Pegoku/buckshot-roulette-irl/images/explosions/Explosion-2.png

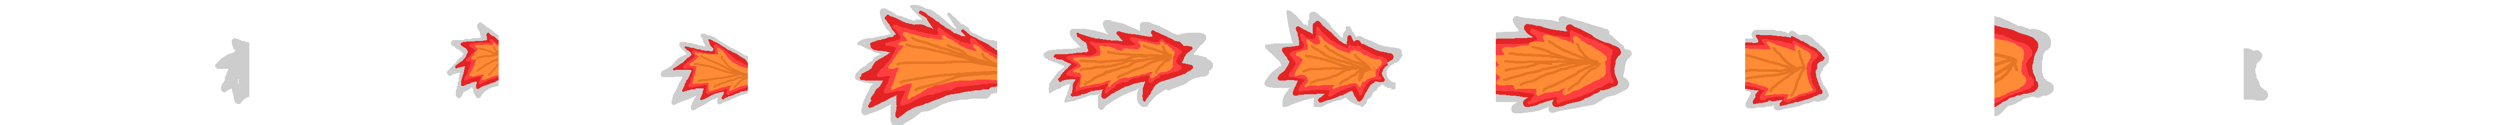
images/explosions/Explosion-2.png
