Pegoku/buckshot-roulette-irl/images/soup's/soup-blue-1.png

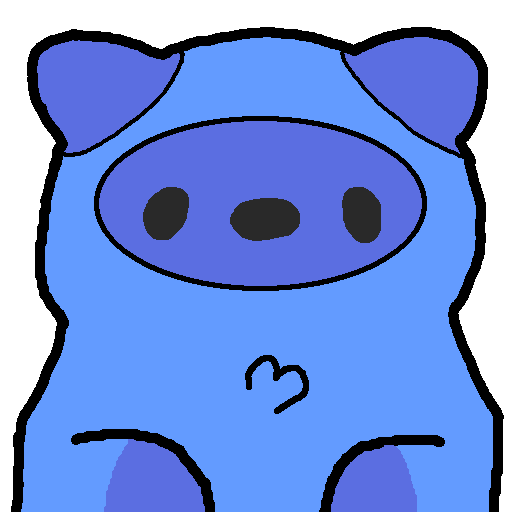
images/soup's/soup-blue-1.png
