Pegoku/buckshot-roulette-irl/images/soup's/soup-blue-2.png

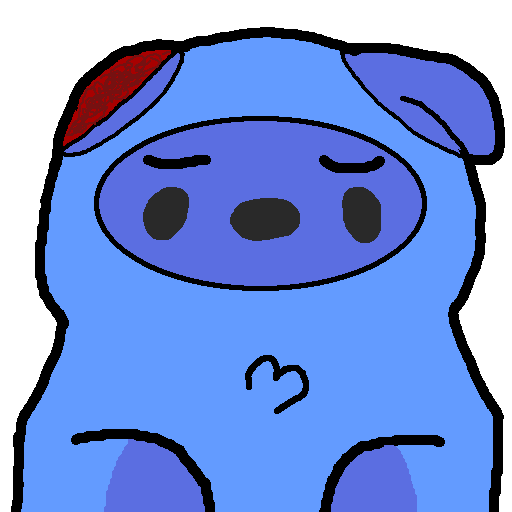
images/soup's/soup-blue-2.png
