Pegoku/buckshot-roulette-irl/images/soup's/soup-blue-4.png

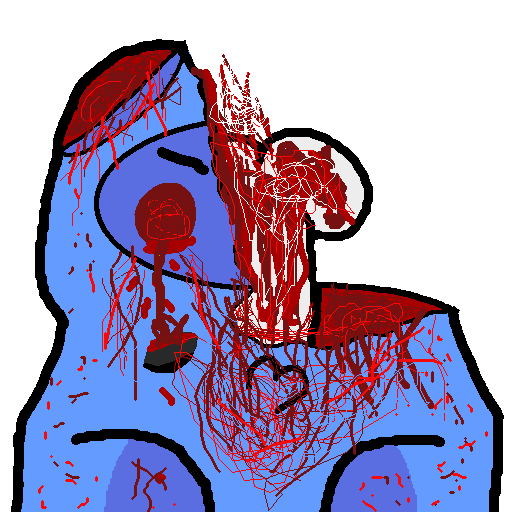
images/soup's/soup-blue-4.png
