Pegoku/buckshot-roulette-irl/images/soup's/soup-yellow-1.png

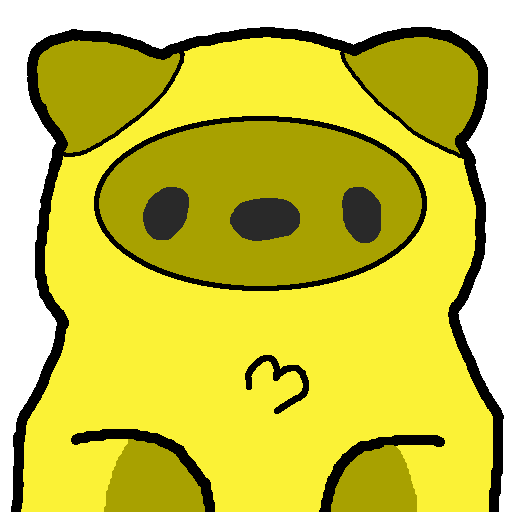
images/soup's/soup-yellow-1.png
