Pegoku/buckshot-roulette-irl/images/soup's/soup-yellow-4.png

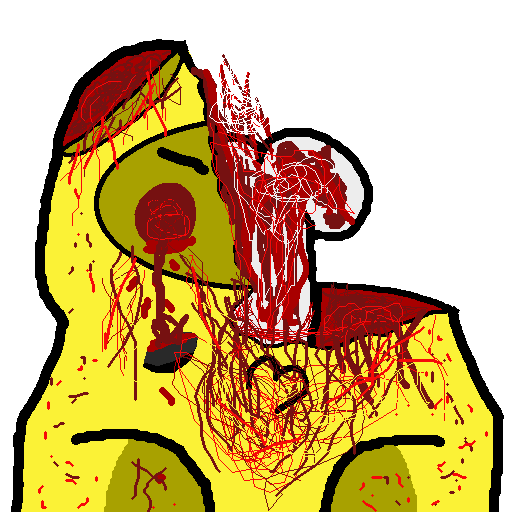
images/soup's/soup-yellow-4.png
