Pegoku/buckshot-roulette-irl/models/PRINTS-CORRECT-SIZE/phone.stl

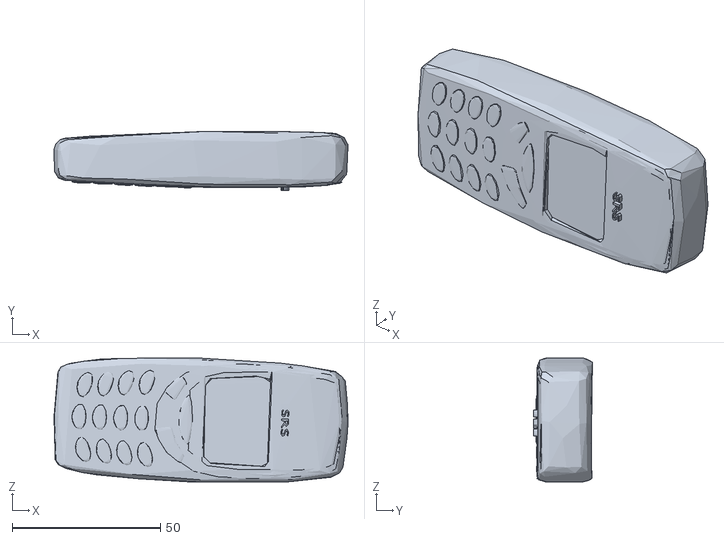
[picture p29: CAD file, 2026-07-05]
models/PRINTS-CORRECT-SIZE/phone.stl
99.2 x 20.0 x 41.8
