Pegoku/buckshot-roulette-irl/models/PRINTS-CORRECT-SIZE/magnifying-glass.stl

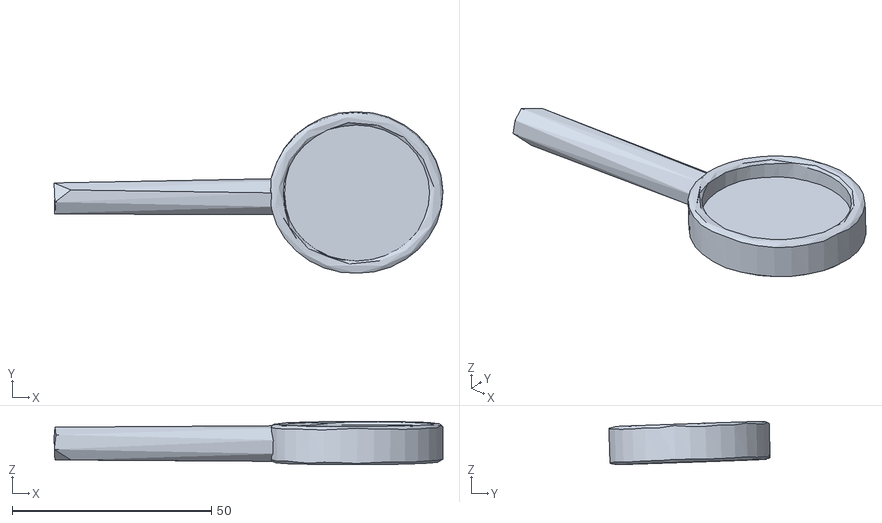
[picture p30: CAD file, 2026-07-05]
models/PRINTS-CORRECT-SIZE/magnifying-glass.stl
97.7 x 40.5 x 10.9
