Pegoku/buckshot-roulette-irl/models/PRINTS-CORRECT-SIZE/pump-handle-part1.stl

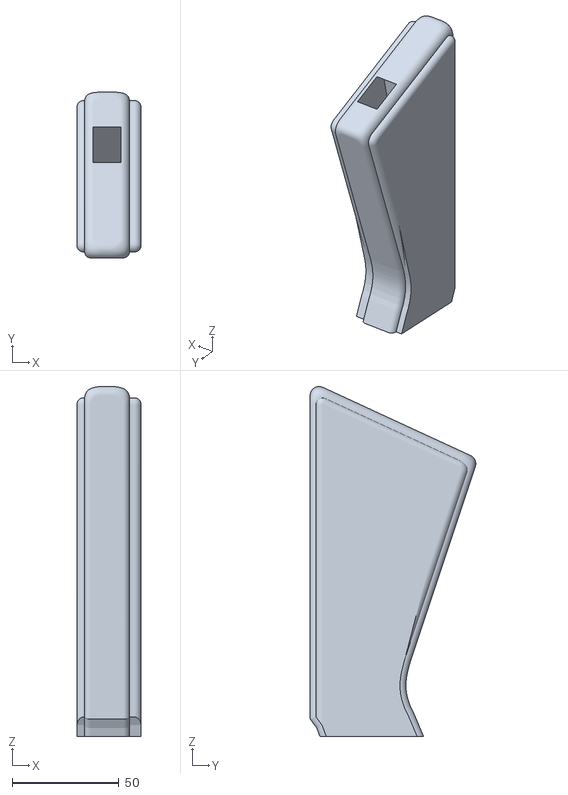
[picture p31: CAD file, 2026-07-05]
models/PRINTS-CORRECT-SIZE/pump-handle-part1.stl
30.0 x 77.7 x 164.0
