Pegoku/buckshot-roulette-irl/models/PRINTS-CORRECT-SIZE/hlaven.stl

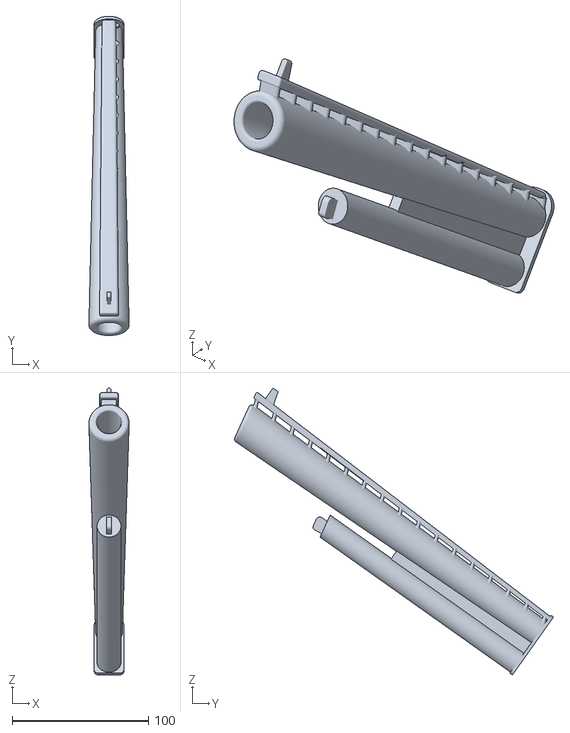
[picture p32: CAD file, 2026-07-05]
models/PRINTS-CORRECT-SIZE/hlaven.stl
29.5 x 233.7 x 210.2
