Pegoku/buckshot-roulette-irl/models/PRINTS-CORRECT-SIZE/Handsaw keychain.stl

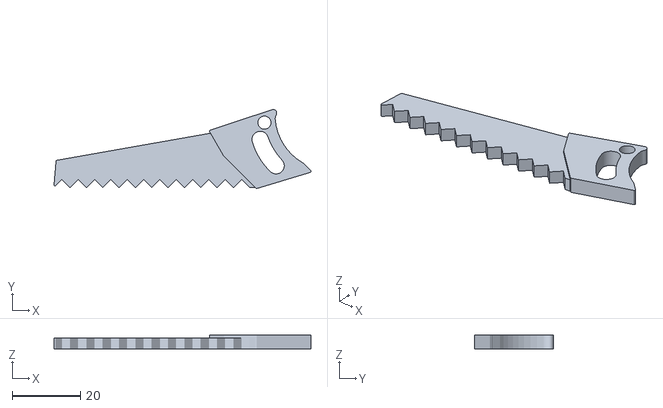
[picture p33: CAD file, 2026-07-05]
models/PRINTS-CORRECT-SIZE/Handsaw keychain.stl
75.5 x 23.2 x 4.00
