Pegoku/buckshot-roulette-irl/models/PRINTS-CORRECT-SIZE/pump-handle-part2.stl

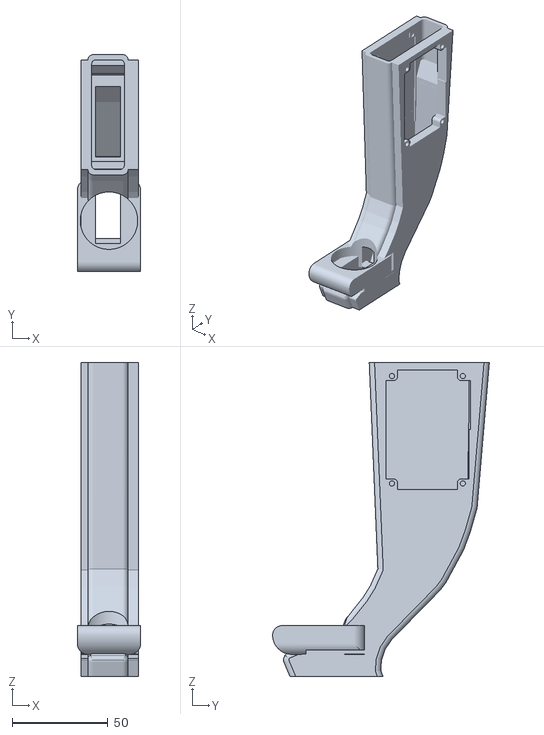
[picture p34: CAD file, 2026-07-05]
models/PRINTS-CORRECT-SIZE/pump-handle-part2.stl
33.0 x 113.2 x 164.0
